xuejun7777/Comprehensive-Design-and-Practice-Project-A---Digital-Thermometer-Based-on-NTC/NTC/gerber/NTC-F_Mask.pdf

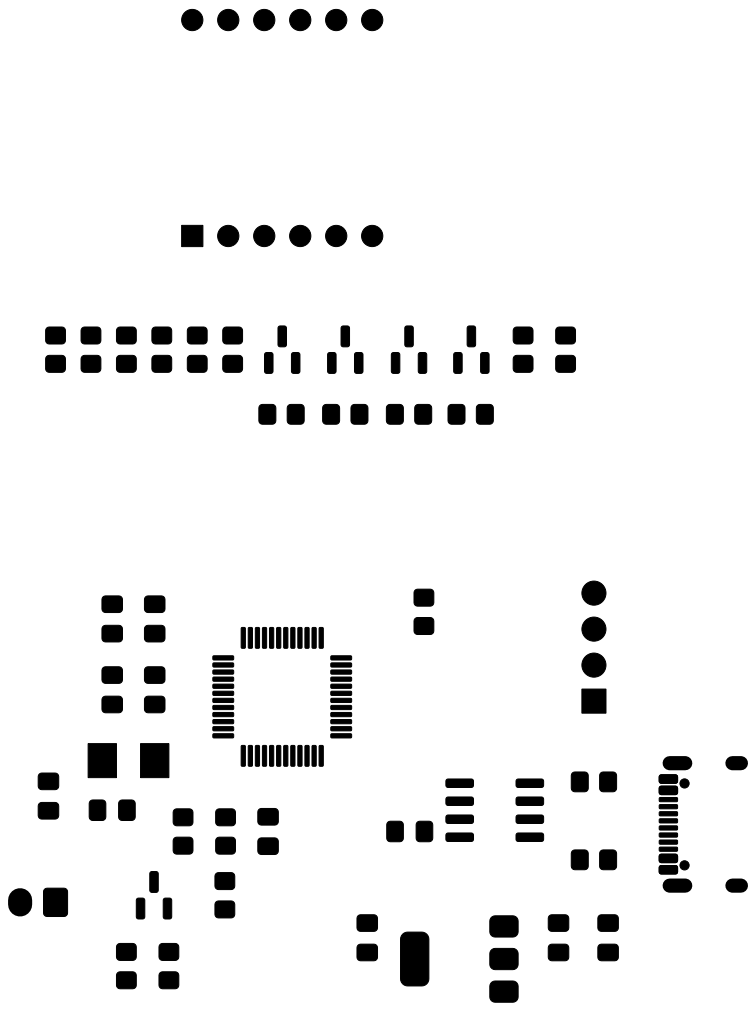
[picture p23: page 1]
