xuejun7777/Comprehensive-Design-and-Practice-Project-A---Digital-Thermometer-Based-on-NTC/NTC/gerber/NTC-F_Paste.pdf

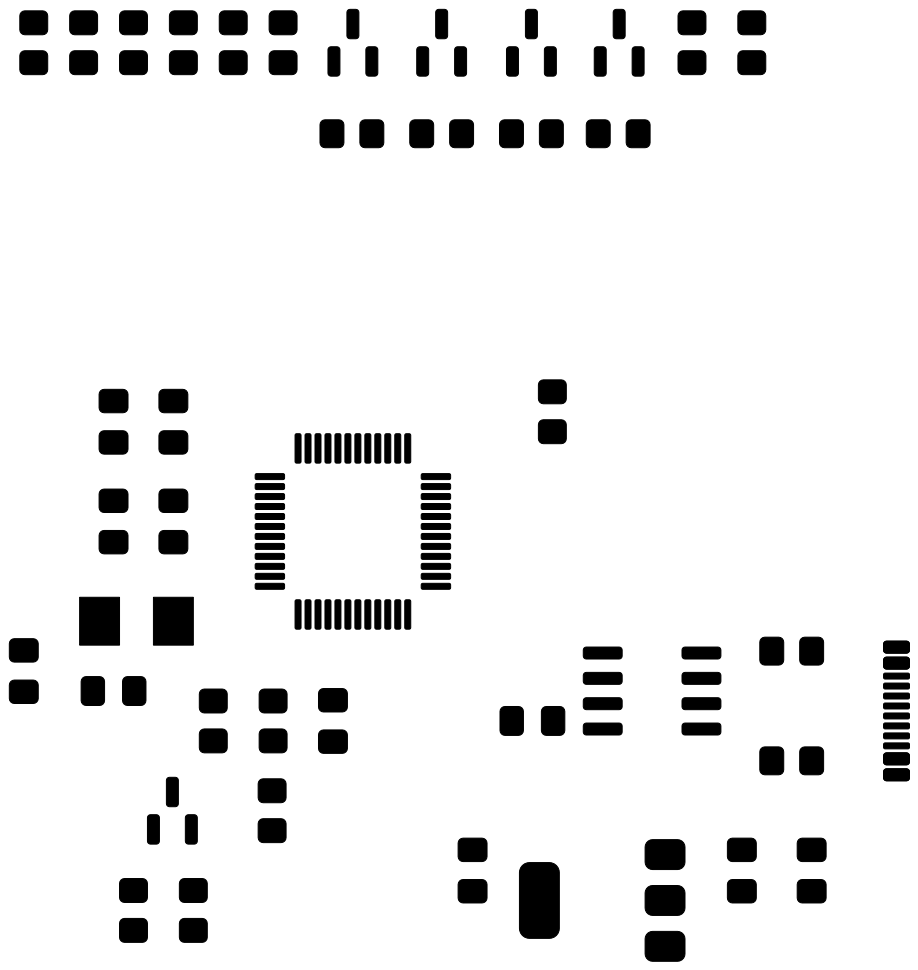
[picture p24: page 1]
