xuejun7777/Comprehensive-Design-and-Practice-Project-A---Digital-Thermometer-Based-on-NTC/NTC/gerber/NTC-F_Silkscreen.pdf

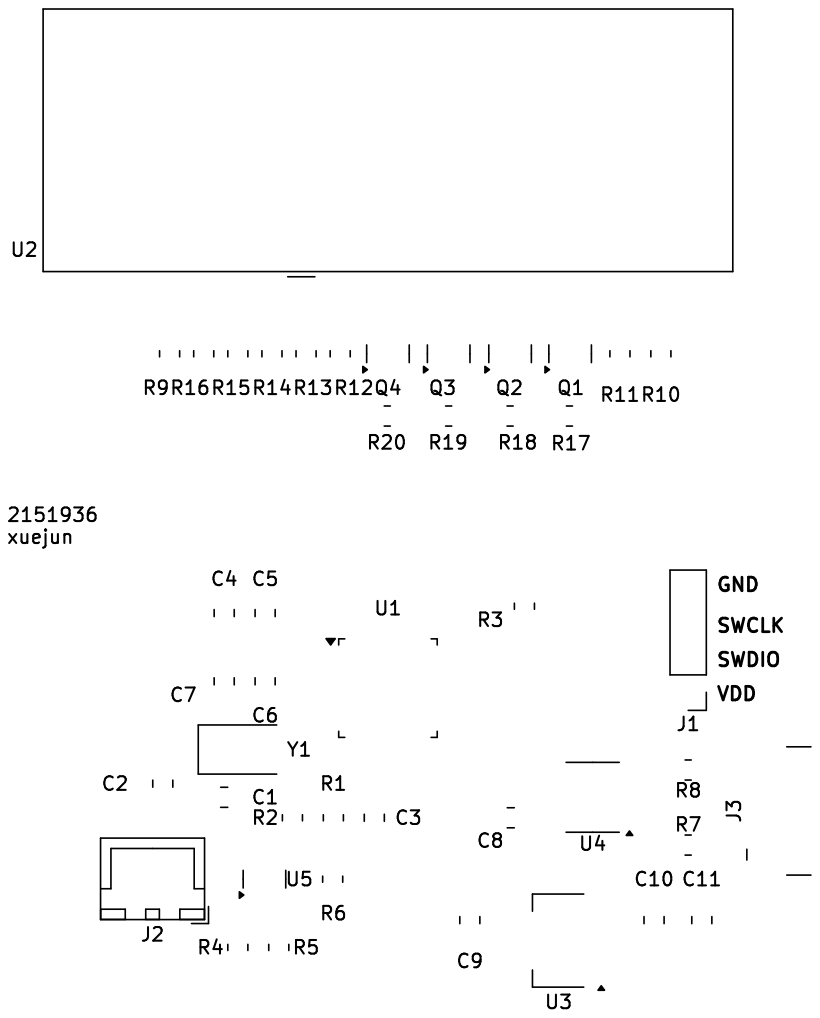
[picture p25: page 1]
