xuejun7777/Comprehensive-Design-and-Practice-Project-A---Digital-Thermometer-Based-on-NTC/NTC/pcb_pdf/NTC-B_Cu.pdf

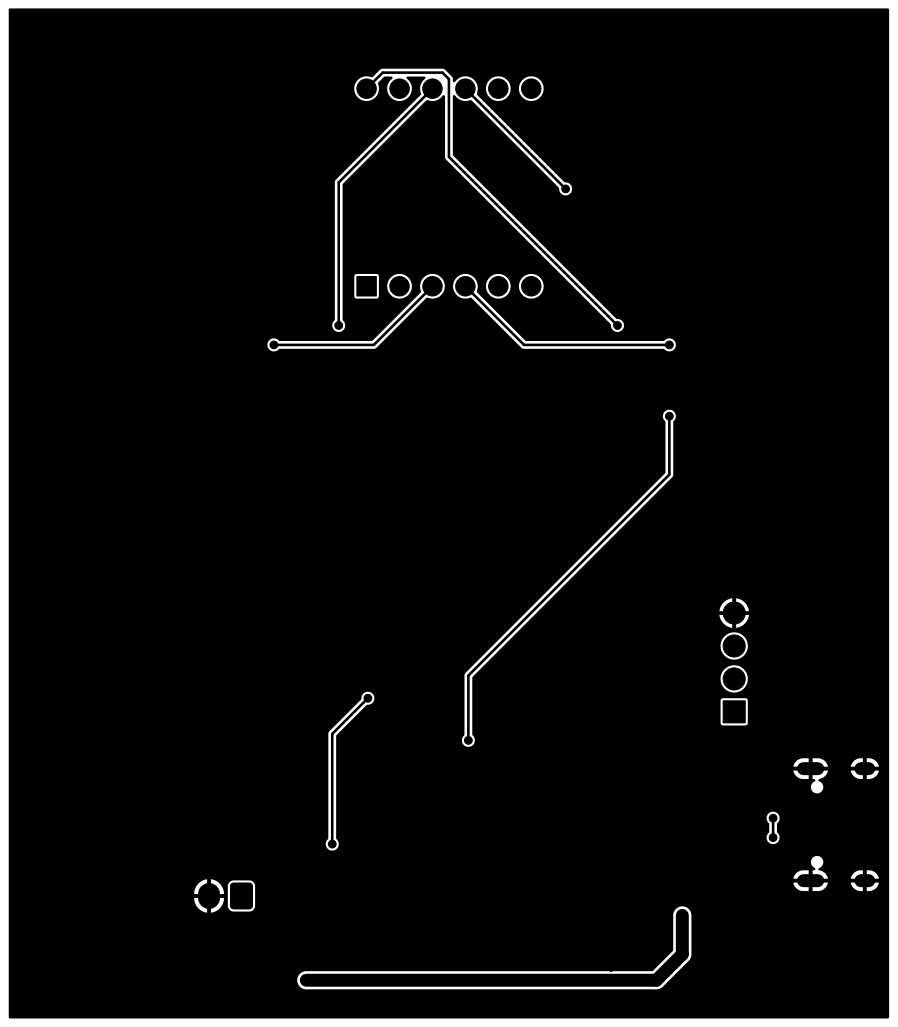
[picture p26: page 1]
