xuejun7777/Comprehensive-Design-and-Practice-Project-A---Digital-Thermometer-Based-on-NTC/NTC/pcb_pdf/NTC-F_Cu.pdf

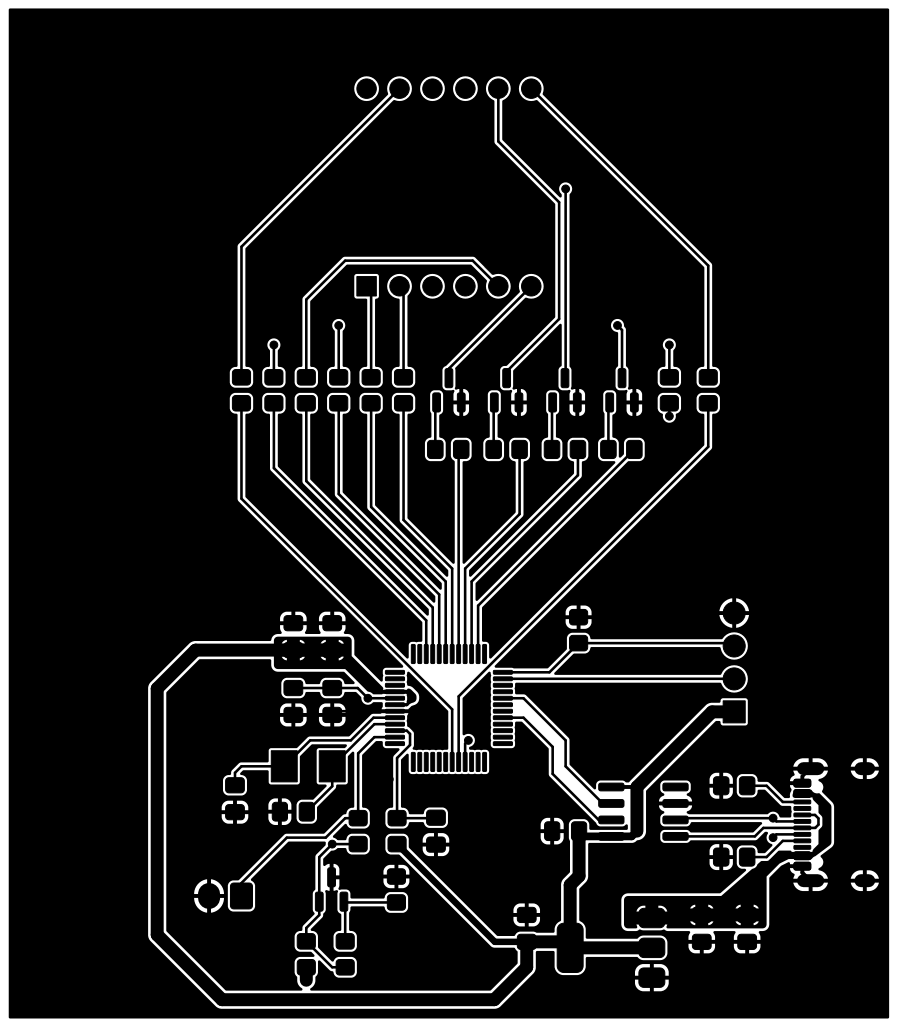
[picture p27: page 1]
