xuejun7777/Comprehensive-Design-and-Practice-Project-A---Digital-Thermometer-Based-on-NTC/NTC2/pcb_pdf/NTC-B_Cu.pdf

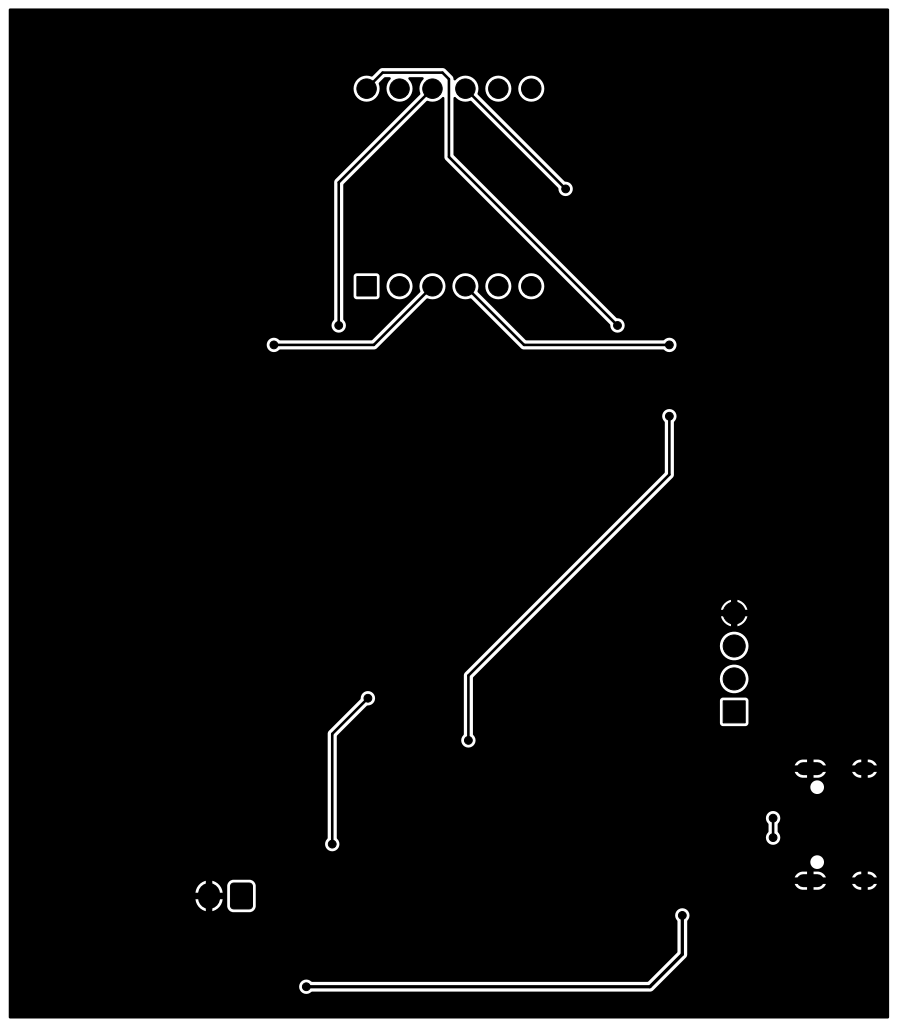
[picture p28: page 1]
