xuejun7777/Comprehensive-Design-and-Practice-Project-A---Digital-Thermometer-Based-on-NTC/NTC2/pcb_pdf/NTC-B_Mask.pdf

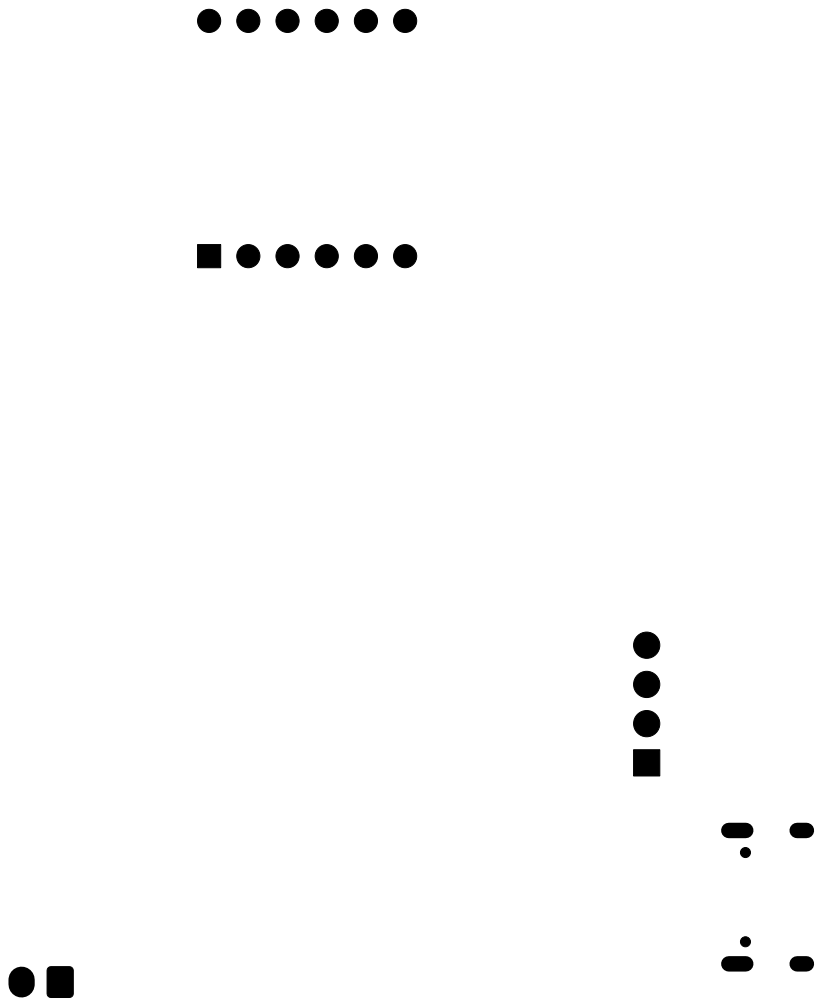
[picture p29: page 1]
