xuejun7777/Comprehensive-Design-and-Practice-Project-A---Digital-Thermometer-Based-on-NTC/NTC2/pcb_pdf/NTC-F_Cu.pdf

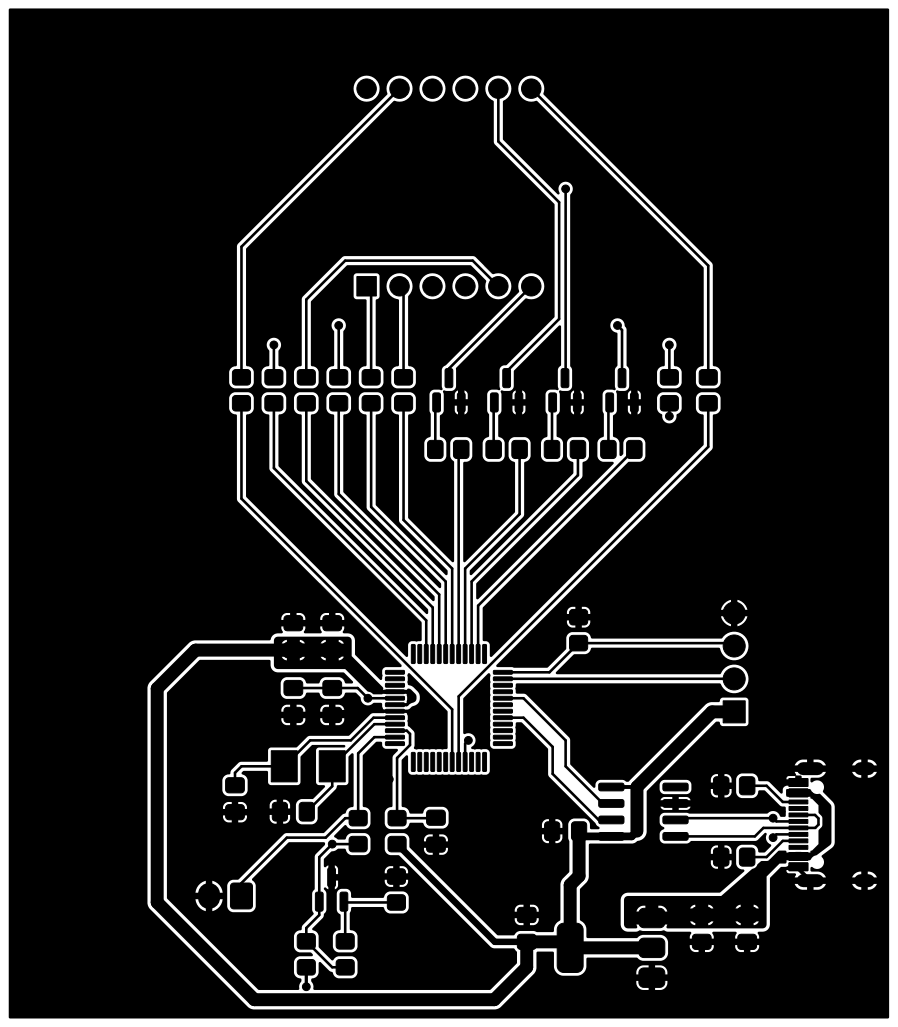
[picture p30: page 1]
