xuejun7777/Comprehensive-Design-and-Practice-Project-A---Digital-Thermometer-Based-on-NTC/NTC2/pcb_pdf/NTC-F_Paste.pdf

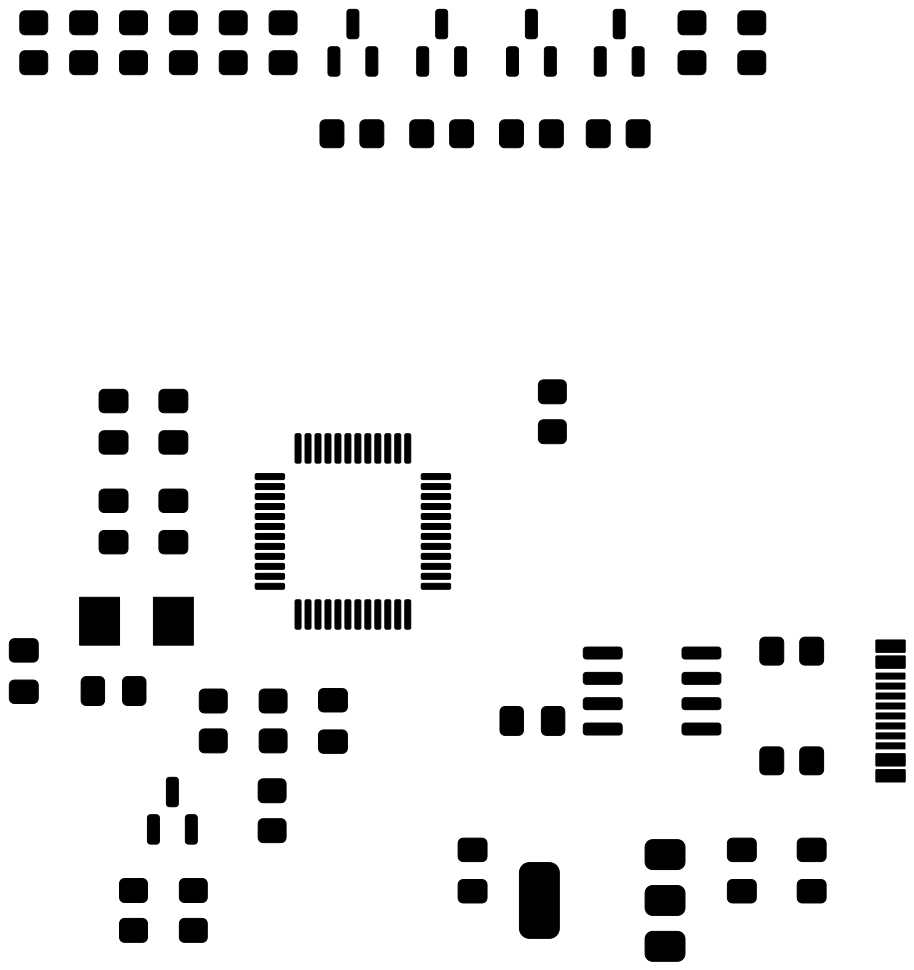
[picture p32: page 1]
